ggh-png/Wls-sullivan/MR_2_UI/Image/backward.png

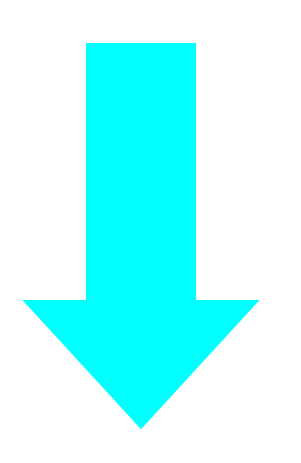
MR_2_UI/Image/backward.png
