ggh-png/Wls-sullivan/MR_2_UI/Image/forward.png

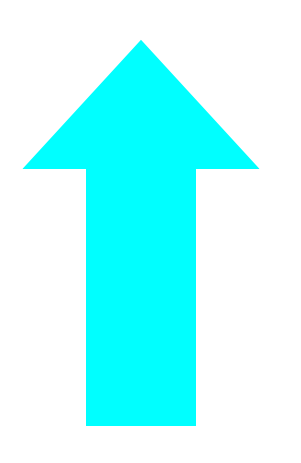
MR_2_UI/Image/forward.png
