ggh-png/Wls-sullivan/MR_2_UI/Image/painful.png

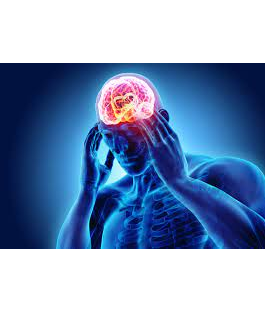
MR_2_UI/Image/painful.png
