ggh-png/Wls-sullivan/MR_2_UI/Image/right.png

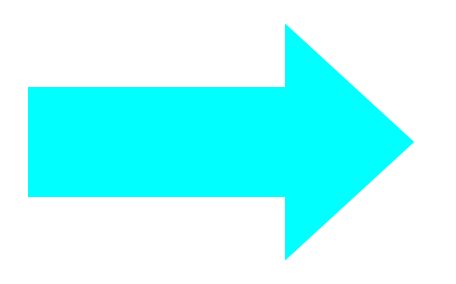
MR_2_UI/Image/right.png
