ggh-png/Wls-sullivan/MR_2_UI/Image/sleep.png

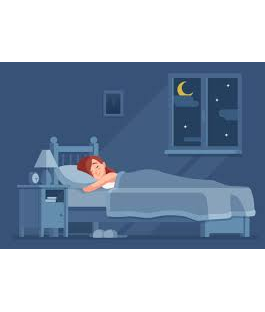
MR_2_UI/Image/sleep.png
