ggh-png/Wls-sullivan/MR_2_UI/Image/stop.png

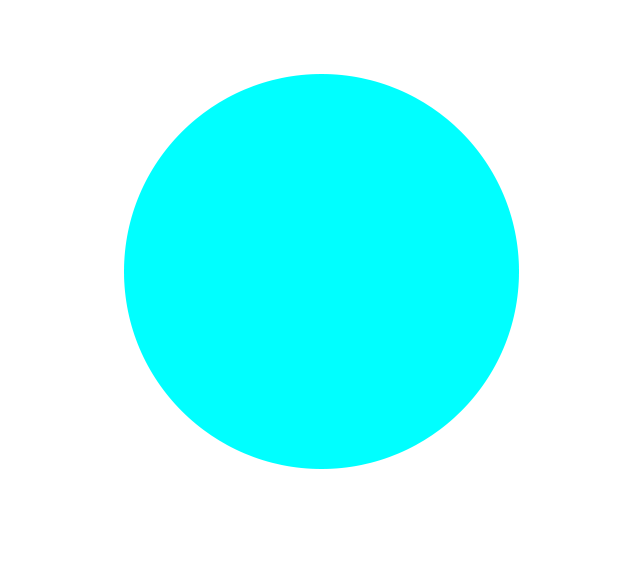
MR_2_UI/Image/stop.png
