ggh-png/Wls-sullivan/MR_2_UI/Image/toilet.png

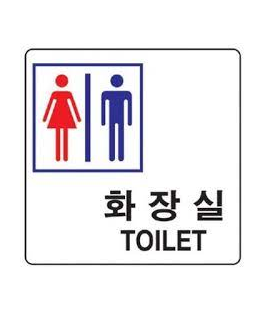
MR_2_UI/Image/toilet.png
