ggh-png/Wls-sullivan/MR_2_mobile/MR_2_motor_control/ros_lib/play_motion_builder_msgs/BuildMotionActionFeedback.h

#ifndef _ROS_play_motion_builder_msgs_BuildMotionActionFeedback_h
#define _ROS_play_motion_builder_msgs_BuildMotionActionFeedback_h

#include <stdint.h>
#include <string.h>
#include <stdlib.h>
#include "ros/msg.h"
#include "std_msgs/Header.h"
#include "actionlib_msgs/GoalStatus.h"
#include "play_motion_builder_msgs/BuildMotionFeedback.h"

namespace play_motion_builder_msgs
{

  class BuildMotionActionFeedback : public ros::Msg
  {
    public:
      typedef std_msgs::Header _header_type;
      _header_type header;
      typedef actionlib_msgs::GoalStatus _status_type;
      _status_type status;
      typedef play_motion_builder_msgs::BuildMotionFeedback _feedback_type;
      _feedback_type feedback;

    BuildMotionActionFeedback():
      header(),
      status(),
      feedback()
    {
    }

    virtual int serialize(unsigned char *outbuffer) const
    {
      int offset = 0;
      offset += this->header.serialize(outbuffer + offset);
      offset += this->status.serialize(outbuffer + offset);
      offset += this->feedback.serialize(outbuffer + offset);
      return offset;
    }

    virtual int deserialize(unsigned char *inbuffer)
    {
      int offset = 0;
      offset += this->header.deserialize(inbuffer + offset);
      offset += this->status.deserialize(inbuffer + offset);
      offset += this->feedback.deserialize(inbuffer + offset);
     return offset;
    }

    const char * getType(){ return "play_motion_builder_msgs/BuildMotionActionFeedback"; };
    const char * getMD5(){ return "aae20e09065c3809e8a8e87c4c8953fd"; };

  };

}
#endif
