ggh-png/Wls-sullivan/MR_2_mobile/MR_2_motor_control/ros_lib/play_motion_msgs/PlayMotionResult.h

#ifndef _ROS_play_motion_msgs_PlayMotionResult_h
#define _ROS_play_motion_msgs_PlayMotionResult_h

#include <stdint.h>
#include <string.h>
#include <stdlib.h>
#include "ros/msg.h"

namespace play_motion_msgs
{

  class PlayMotionResult : public ros::Msg
  {
    public:
      typedef int32_t _error_code_type;
      _error_code_type error_code;
      typedef const char* _error_string_type;
      _error_string_type error_string;
      enum { SUCCEEDED =  1 };
      enum { MOTION_NOT_FOUND =  -1 };
      enum { CONTROLLER_BUSY =  -3 };
      enum { MISSING_CONTROLLER =  -4 };
      enum { TRAJECTORY_ERROR =  -5 };
      enum { GOAL_NOT_REACHED =  -6 };
      enum { PLANNER_OFFLINE =  -7 };
      enum { NO_PLAN_FOUND =  -8 };
      enum { OTHER_ERROR =  -42 };

    PlayMotionResult():
      error_code(0),
      error_string("")
    {
    }

    virtual int serialize(unsigned char *outbuffer) const
    {
      int offset = 0;
      union {
        int32_t real;
        uint32_t base;
      } u_error_code;
      u_error_code.real = this->error_code;
      *(outbuffer + offset + 0) = (u_error_code.base >> (8 * 0)) & 0xFF;
      *(outbuffer + offset + 1) = (u_error_code.base >> (8 * 1)) & 0xFF;
      *(outbuffer + offset + 2) = (u_error_code.base >> (8 * 2)) & 0xFF;
      *(outbuffer + offset + 3) = (u_error_code.base >> (8 * 3)) & 0xFF;
      offset += sizeof(this->error_code);
      uint32_t length_error_string = strlen(this->error_string);
      varToArr(outbuffer + offset, length_error_string);
      offset += 4;
      memcpy(outbuffer + offset, this->error_string, length_error_string);
      offset += length_error_string;
      return offset;
    }

    virtual int deserialize(unsigned char *inbuffer)
    {
      int offset = 0;
      union {
        int32_t real;
        uint32_t base;
      } u_error_code;
      u_error_code.base = 0;
      u_error_code.base |= ((uint32_t) (*(inbuffer + offset + 0))) << (8 * 0);
      u_error_code.base |= ((uint32_t) (*(inbuffer + offset + 1))) << (8 * 1);
      u_error_code.base |= ((uint32_t) (*(inbuffer + offset + 2))) << (8 * 2);
      u_error_code.base |= ((uint32_t) (*(inbuffer + offset + 3))) << (8 * 3);
      this->error_code = u_error_code.real;
      offset += sizeof(this->error_code);
      uint32_t length_error_string;
      arrToVar(length_error_string, (inbuffer + offset));
      offset += 4;
      for(unsigned int k= offset; k< offset+length_error_string; ++k){
          inbuffer[k-1]=inbuffer[k];
      }
      inbuffer[offset+length_error_string-1]=0;
      this->error_string = (char *)(inbuffer + offset-1);
      offset += length_error_string;
     return offset;
    }

    const char * getType(){ return "play_motion_msgs/PlayMotionResult"; };
    const char * getMD5(){ return "5560cb9a7211cb4b5a730f6f07ec124b"; };

  };

}
#endif
