ggh-png/Wls-sullivan/MR_2_mobile/MR_2_motor_control/ros_lib/variant_msgs/Variant.h

#ifndef _ROS_variant_msgs_Variant_h
#define _ROS_variant_msgs_Variant_h

#include <stdint.h>
#include <string.h>
#include <stdlib.h>
#include "ros/msg.h"
#include "variant_msgs/VariantHeader.h"
#include "variant_msgs/VariantType.h"

namespace variant_msgs
{

  class Variant : public ros::Msg
  {
    public:
      typedef variant_msgs::VariantHeader _header_type;
      _header_type header;
      typedef variant_msgs::VariantType _type_type;
      _type_type type;
      uint32_t data_length;
      typedef uint8_t _data_type;
      _data_type st_data;
      _data_type * data;

    Variant():
      header(),
      type(),
      data_length(0), data(NULL)
    {
    }

    virtual int serialize(unsigned char *outbuffer) const
    {
      int offset = 0;
      offset += this->header.serialize(outbuffer + offset);
      offset += this->type.serialize(outbuffer + offset);
      *(outbuffer + offset + 0) = (this->data_length >> (8 * 0)) & 0xFF;
      *(outbuffer + offset + 1) = (this->data_length >> (8 * 1)) & 0xFF;
      *(outbuffer + offset + 2) = (this->data_length >> (8 * 2)) & 0xFF;
      *(outbuffer + offset + 3) = (this->data_length >> (8 * 3)) & 0xFF;
      offset += sizeof(this->data_length);
      for( uint32_t i = 0; i < data_length; i++){
      *(outbuffer + offset + 0) = (this->data[i] >> (8 * 0)) & 0xFF;
      offset += sizeof(this->data[i]);
      }
      return offset;
    }

    virtual int deserialize(unsigned char *inbuffer)
    {
      int offset = 0;
      offset += this->header.deserialize(inbuffer + offset);
      offset += this->type.deserialize(inbuffer + offset);
      uint32_t data_lengthT = ((uint32_t) (*(inbuffer + offset))); 
      data_lengthT |= ((uint32_t) (*(inbuffer + offset + 1))) << (8 * 1); 
      data_lengthT |= ((uint32_t) (*(inbuffer + offset + 2))) << (8 * 2); 
      data_lengthT |= ((uint32_t) (*(inbuffer + offset + 3))) << (8 * 3); 
      offset += sizeof(this->data_length);
      if(data_lengthT > data_length)
        this->data = (uint8_t*)realloc(this->data, data_lengthT * sizeof(uint8_t));
      data_length = data_lengthT;
      for( uint32_t i = 0; i < data_length; i++){
      this->st_data =  ((uint8_t) (*(inbuffer + offset)));
      offset += sizeof(this->st_data);
        memcpy( &(this->data[i]), &(this->st_data), sizeof(uint8_t));
      }
     return offset;
    }

    const char * getType(){ return "variant_msgs/Variant"; };
    const char * getMD5(){ return "01c24cd44ef34b0c6a309bcafb6bdfab"; };

  };

}
#endif
