ggh-png/Wls-sullivan/MR_2_mobile/MR_2_motor_control/ros_lib/variant_msgs/VariantHeader.h

#ifndef _ROS_variant_msgs_VariantHeader_h
#define _ROS_variant_msgs_VariantHeader_h

#include <stdint.h>
#include <string.h>
#include <stdlib.h>
#include "ros/msg.h"

namespace variant_msgs
{

  class VariantHeader : public ros::Msg
  {
    public:
      typedef const char* _publisher_type;
      _publisher_type publisher;
      typedef const char* _topic_type;
      _topic_type topic;
      typedef bool _latched_type;
      _latched_type latched;

    VariantHeader():
      publisher(""),
      topic(""),
      latched(0)
    {
    }

    virtual int serialize(unsigned char *outbuffer) const
    {
      int offset = 0;
      uint32_t length_publisher = strlen(this->publisher);
      varToArr(outbuffer + offset, length_publisher);
      offset += 4;
      memcpy(outbuffer + offset, this->publisher, length_publisher);
      offset += length_publisher;
      uint32_t length_topic = strlen(this->topic);
      varToArr(outbuffer + offset, length_topic);
      offset += 4;
      memcpy(outbuffer + offset, this->topic, length_topic);
      offset += length_topic;
      union {
        bool real;
        uint8_t base;
      } u_latched;
      u_latched.real = this->latched;
      *(outbuffer + offset + 0) = (u_latched.base >> (8 * 0)) & 0xFF;
      offset += sizeof(this->latched);
      return offset;
    }

    virtual int deserialize(unsigned char *inbuffer)
    {
      int offset = 0;
      uint32_t length_publisher;
      arrToVar(length_publisher, (inbuffer + offset));
      offset += 4;
      for(unsigned int k= offset; k< offset+length_publisher; ++k){
          inbuffer[k-1]=inbuffer[k];
      }
      inbuffer[offset+length_publisher-1]=0;
      this->publisher = (char *)(inbuffer + offset-1);
      offset += length_publisher;
      uint32_t length_topic;
      arrToVar(length_topic, (inbuffer + offset));
      offset += 4;
      for(unsigned int k= offset; k< offset+length_topic; ++k){
          inbuffer[k-1]=inbuffer[k];
      }
      inbuffer[offset+length_topic-1]=0;
      this->topic = (char *)(inbuffer + offset-1);
      offset += length_topic;
      union {
        bool real;
        uint8_t base;
      } u_latched;
      u_latched.base = 0;
      u_latched.base |= ((uint8_t) (*(inbuffer + offset + 0))) << (8 * 0);
      this->latched = u_latched.real;
      offset += sizeof(this->latched);
     return offset;
    }

    const char * getType(){ return "variant_msgs/VariantHeader"; };
    const char * getMD5(){ return "e4adbe277ed51d50644d64067b86c73d"; };

  };

}
#endif
